krzys9876/keyb_15x5/layout/keyb_15x5.jpg

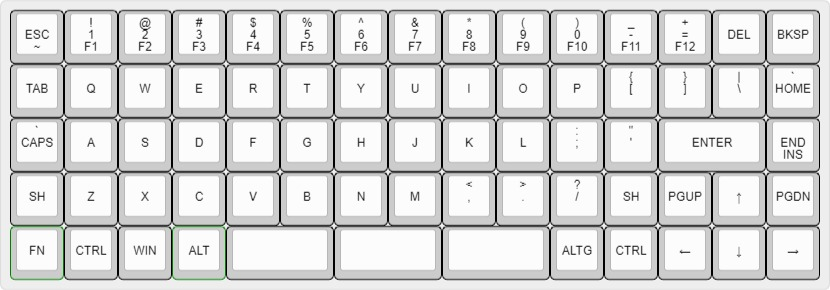
layout/keyb_15x5.jpg
